Xevel/usb2lds/firmware/usb2lds/time.h

/*
 * time.h
 *
 * Created: 28/01/2014 15:11:47
 *  Author: Xevel
 */ 


#ifndef TIME_H_
#define TIME_H_
#include "common.h"

void micros_init();
uint16_t micros();
uint16_t micros_reset();

#endif /* TIME_H_ */
